skaman82/Pocket-Groundstation/3D files/Cinema4D files/tex/Bildschirmfoto 2018-06-30 um 21.27.20.png

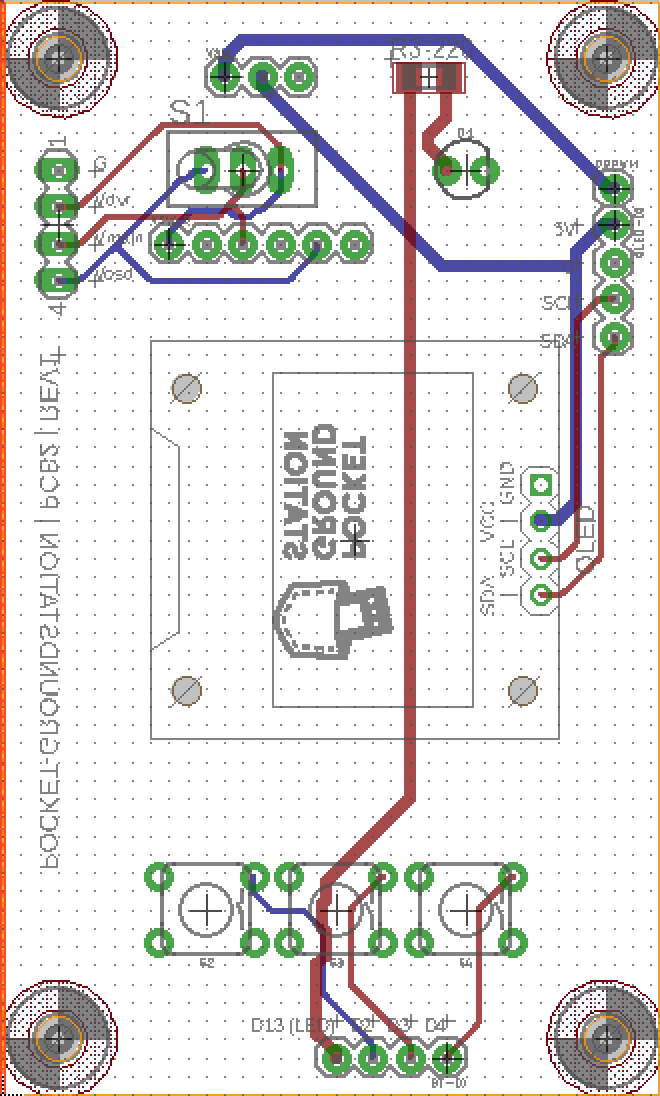
3D files/Cinema4D files/tex/Bildschirmfoto 2018-06-30 um 21.27.20.png
