skaman82/Pocket-Groundstation/3D files/Cinema4D files/tex/Bildschirmfoto 2018-07-01 um 21.55.06.png

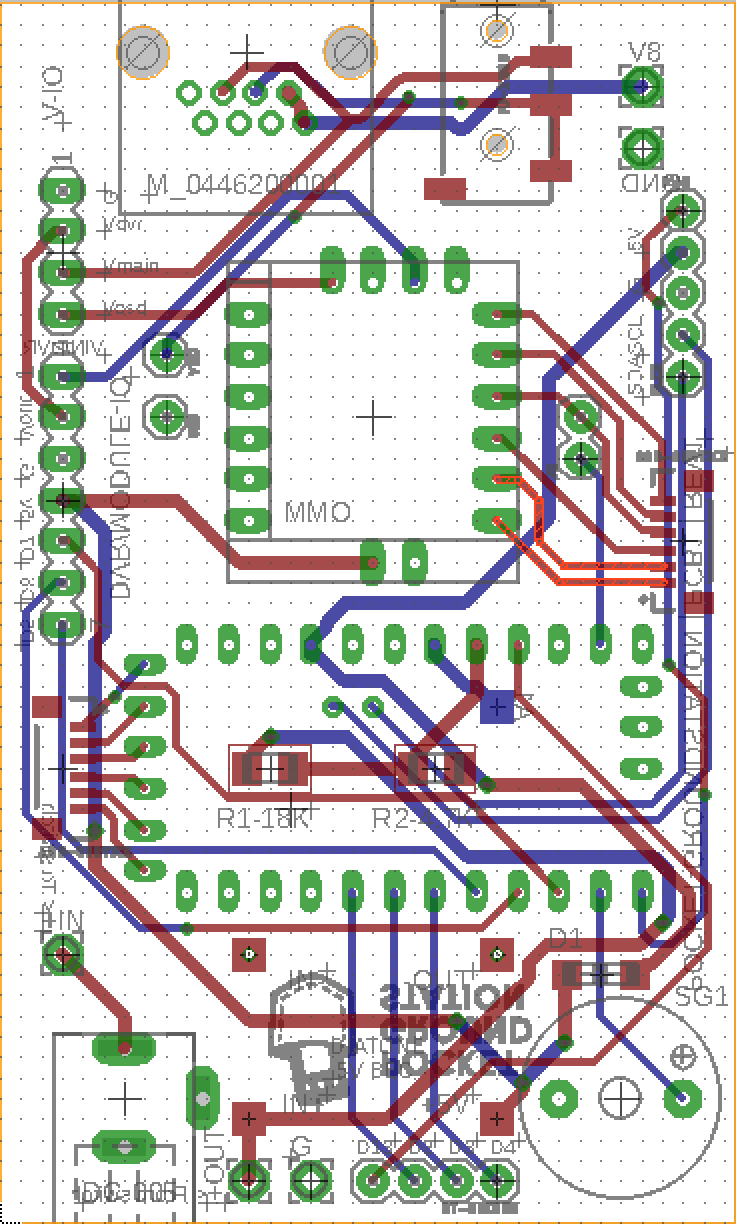
3D files/Cinema4D files/tex/Bildschirmfoto 2018-07-01 um 21.55.06.png
