skaman82/Pocket-Groundstation/3D files/Cinema4D files/tex/Bildschirmfoto 2018-07-02 um 12.51.13.png

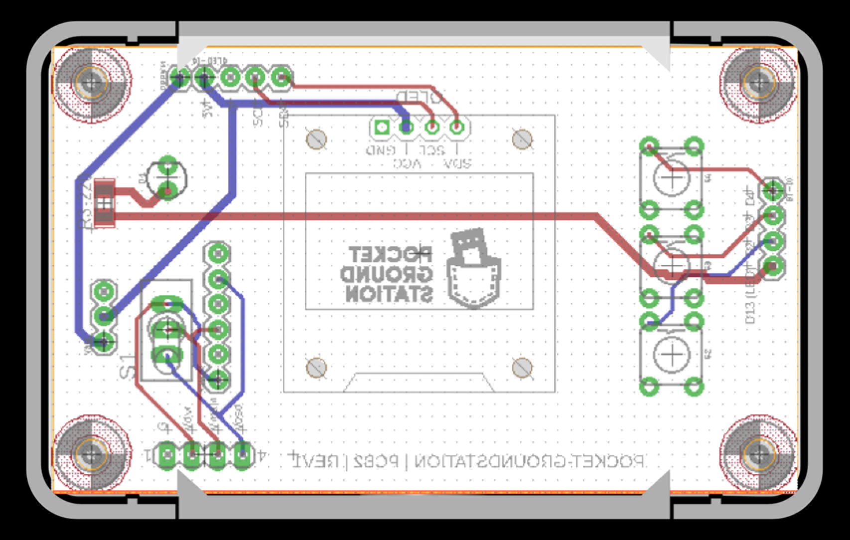
3D files/Cinema4D files/tex/Bildschirmfoto 2018-07-02 um 12.51.13.png
