skaman82/Pocket-Groundstation/3D files/Cinema4D files/tex/downImg.png

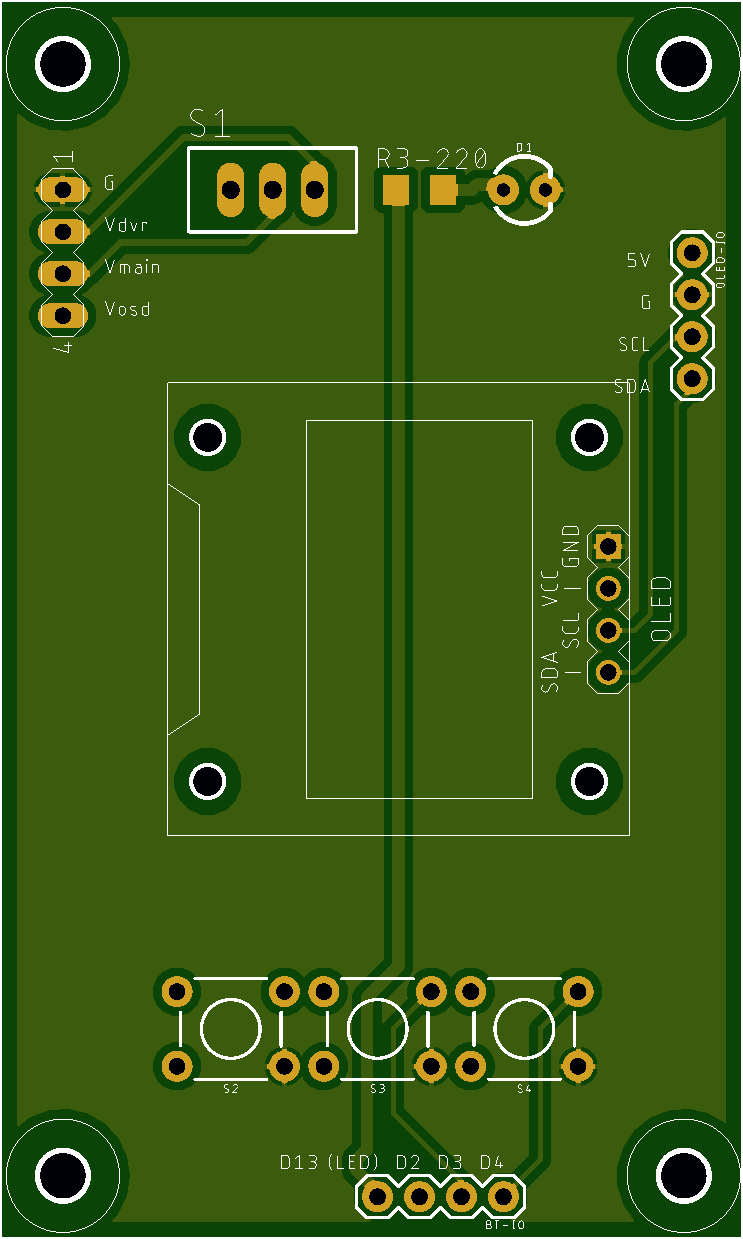
3D files/Cinema4D files/tex/downImg.png
