skaman82/Pocket-Groundstation/OSD-Code/max7456library/examples/CharsetLoader/charset.bmp

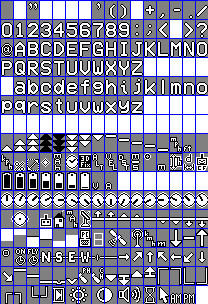
OSD-Code/max7456library/examples/CharsetLoader/charset.bmp
