skaman82/Pocket-Groundstation/PCB Files/Gerber Files/Module-PCB_v1_t.png

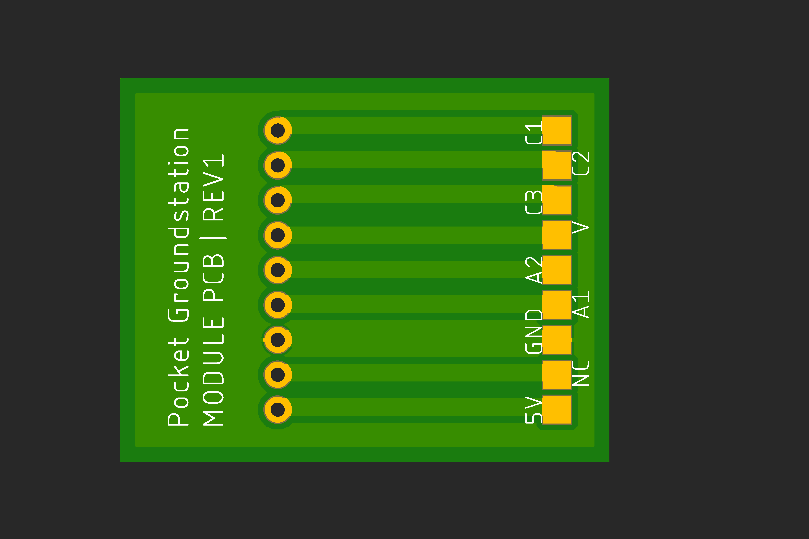
PCB Files/Gerber Files/Module-PCB_v1_t.png
