skaman82/Pocket-Groundstation/PCB Files/Gerber Files/PCB 1_bottom.png

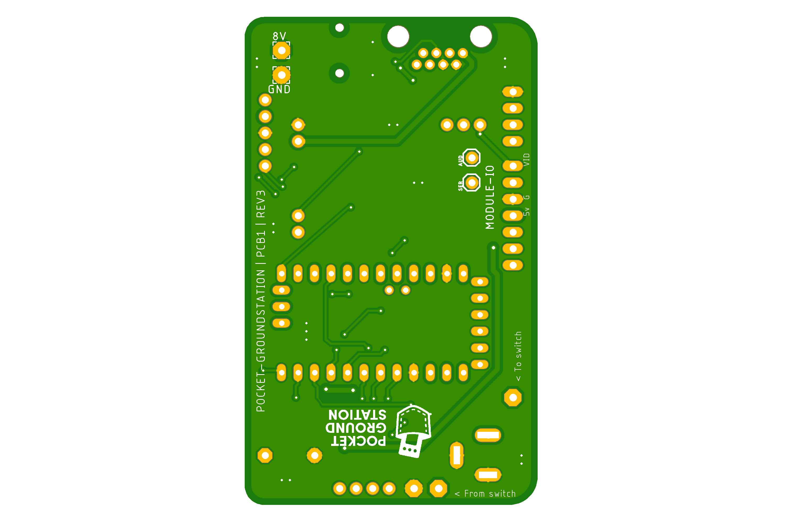
PCB Files/Gerber Files/PCB 1_bottom.png
