skaman82/Pocket-Groundstation/PCB Files/Gerber Files/PCB 1_V2_b.png

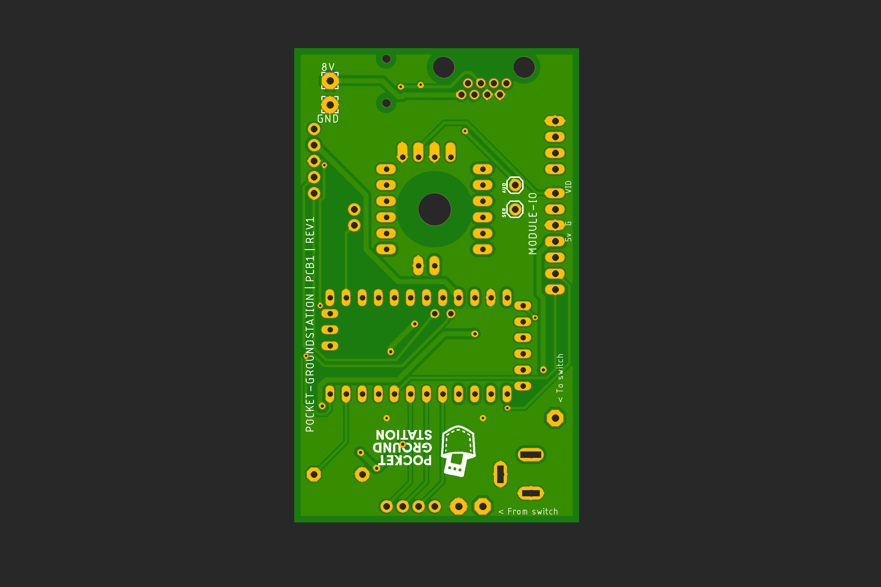
PCB Files/Gerber Files/PCB 1_V2_b.png
