skaman82/Pocket-Groundstation/PCB Files/Gerber Files/PCB 1_V2_t.png

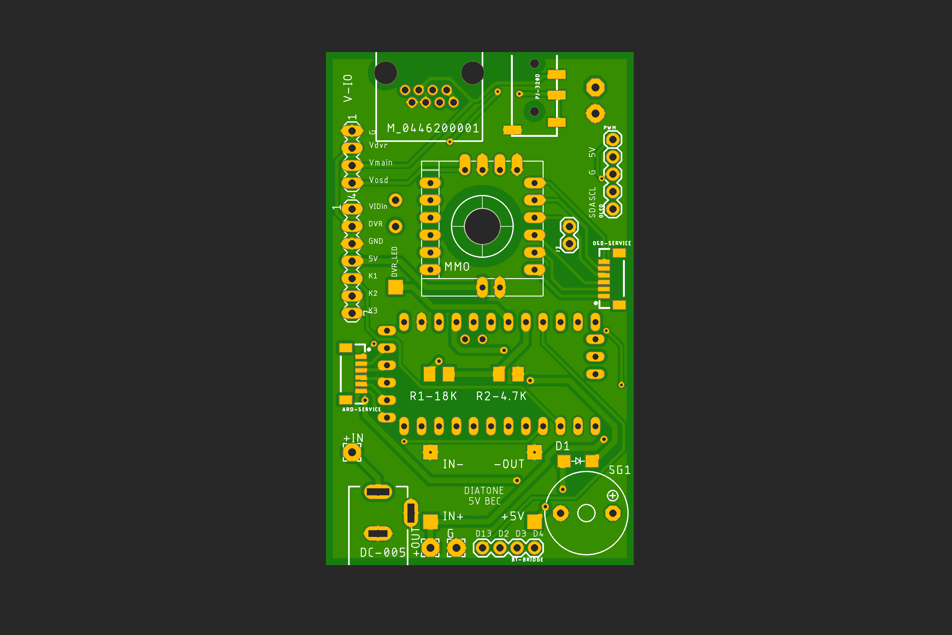
PCB Files/Gerber Files/PCB 1_V2_t.png
