skaman82/Pocket-Groundstation/PCB Files/Gerber Files/PCB 2_bottom.png

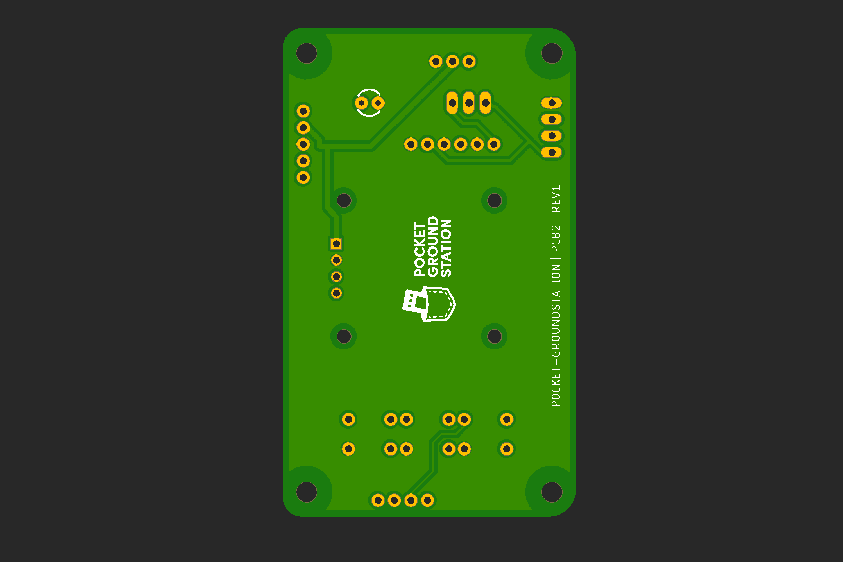
PCB Files/Gerber Files/PCB 2_bottom.png
