skaman82/Pocket-Groundstation/PCB Files/Gerber Files/PCB 2_top.png

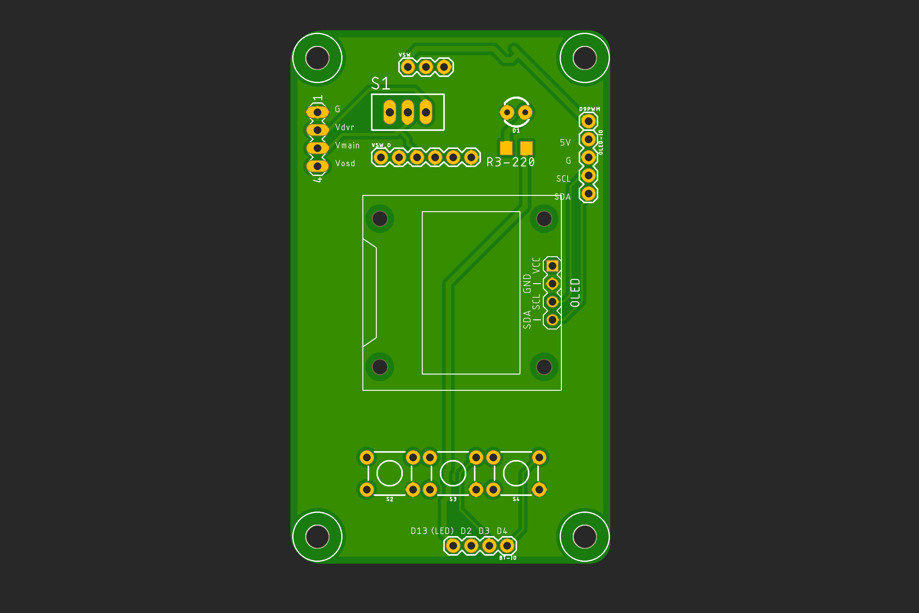
PCB Files/Gerber Files/PCB 2_top.png
