skaman82/Pocket-Groundstation/ARDUINO-Code/bitmaps.h

const unsigned char splash_bitmap[] PROGMEM = 
{
  // size is 96 x 46
  0x00,0x00,0x00,0x00,0x00,0x00,0x00,0x00,0x00,0x00,0x00,0x00, // ................................................................................................
  0x00,0x03,0xC0,0x00,0x00,0x00,0x00,0x00,0x00,0x00,0x00,0x00, // ..............####..............................................................................
  0x00,0x03,0xFE,0x00,0x00,0x00,0x00,0x00,0x00,0x00,0x00,0x00, // ..............#########.........................................................................
  0x00,0x03,0xFF,0xF0,0x00,0x00,0x00,0x00,0x00,0x00,0x00,0x00, // ..............##############....................................................................
  0x00,0x03,0xFF,0xFE,0x00,0x00,0x00,0x00,0x00,0x00,0x00,0x00, // ..............#################.................................................................
  0x00,0x07,0xFF,0xFE,0x00,0x00,0x00,0x00,0x00,0x00,0x00,0x00, // .............##################.................................................................
  0x00,0x07,0x3F,0xFE,0x00,0x00,0x00,0x00,0x00,0x00,0x00,0x00, // .............###..#############.................................................................
  0x00,0x07,0x31,0xFC,0x00,0x00,0x00,0x00,0x00,0x00,0x00,0x00, // .............###..##...#######..................................................................
  0x00,0x07,0xF1,0x9C,0x00,0x00,0x00,0x00,0x00,0x00,0x00,0x00, // .............#######...##..###..................................................................
  0x00,0x07,0xFF,0x9C,0x00,0x00,0x00,0x00,0x00,0x00,0x00,0x00, // .............############..###..................................................................
  0x00,0x0F,0xFF,0xFC,0x00,0x00,0x00,0x00,0x00,0x00,0x00,0x00, // ............##################..................................................................
  0x00,0x0F,0xFF,0xFC,0x00,0x3E,0x1E,0x0F,0x1B,0x3E,0xFE,0x00, // ............##################............#####....####.....####...##.##..#####.#######.........
  0x00,0x0F,0x03,0xF8,0x00,0x3F,0x3F,0x1F,0x9B,0x3E,0xFE,0x00, // ............####......#######.............######..######...######..##.##..#####.#######.........
  0x00,0x0F,0x00,0x78,0x00,0x23,0x63,0xB0,0x9E,0x30,0x10,0x00, // ............####.........####.............#...##.##...###.##....#..####...##.......#............
  0x00,0x0F,0x00,0x78,0x00,0x23,0x61,0xB0,0x1C,0x30,0x10,0x00, // ............####.........####.............#...##.##....##.##.......###....##.......#............
  0x00,0x1E,0x00,0x78,0x00,0x3E,0x41,0xB0,0x1C,0x3E,0x10,0x00, // ...........####..........####.............#####..#.....##.##.......###....#####....#............
  0x00,0x7E,0x00,0x78,0x00,0x3C,0x61,0xB0,0x1E,0x30,0x10,0x00, // .........######..........####.............####...##....##.##.......####...##.......#............
  0x03,0xFE,0x00,0xFE,0x00,0x20,0x73,0x19,0x9F,0x30,0x10,0x00, // ......#########.........#######...........#......###..##...##..##..#####..##.......#............
  0x0F,0xFE,0x00,0xFF,0x80,0x30,0x3F,0x1F,0x9B,0xBE,0x10,0x00, // ....###########.........#########.........##......######...######..##.###.#####....#............
  0x0F,0xFE,0x00,0xFF,0x80,0x00,0x0C,0x06,0x00,0x00,0x00,0x00, // ....###########.........#########...................##.......##.................................
  0x0F,0xFE,0x00,0xFF,0x80,0x00,0x00,0x00,0x00,0x00,0x00,0x00, // ....###########.........#########...............................................................
  0x0C,0x7F,0xFF,0xF1,0x80,0x00,0x00,0x00,0x00,0x00,0x00,0x00, // ....##...###################...##...............................................................
  0x0C,0x00,0xF8,0x01,0x80,0x1F,0x1F,0x0F,0x0C,0xCC,0xCF,0x80, // ....##..........#####..........##..........#####...#####....####....##..##..##..##..#####.......
  0x0D,0x80,0x00,0x05,0x80,0x3F,0x1F,0x9F,0x8C,0xCC,0xCF,0xC0, // ....##.##....................#.##.........######...######..######...##..##..##..##..######......
  0x0C,0x00,0x00,0x01,0x80,0x30,0x19,0xB0,0xCC,0xCE,0xCC,0x60, // ....##.........................##.........##.......##..##.##....##..##..##..###.##..##...##.....
  0x0C,0x00,0x00,0x01,0x80,0x60,0x19,0xB0,0xCC,0xCF,0xCC,0x60, // ....##.........................##........##........##..##.##....##..##..##..######..##...##.....
  0x0C,0x00,0x00,0x01,0x80,0x67,0x9F,0x30,0xCC,0xCF,0xCC,0x60, // ....##.........................##........##..####..#####..##....##..##..##..######..##...##.....
  0x04,0x80,0x00,0x0D,0x80,0x61,0x9E,0x30,0xCC,0xCD,0xCC,0x60, // .....#..#...................##.##........##....##..####...##....##..##..##..##.###..##...##.....
  0x04,0x80,0x00,0x0D,0x80,0x3B,0x9B,0x1D,0xCD,0xCC,0xCC,0xC0, // .....#..#...................##.##.........###.###..##.##...###.###..##.###..##..##..##..##......
  0x04,0x00,0x00,0x01,0x80,0x1F,0x1B,0x0F,0x87,0x8C,0xCF,0xC0, // .....#.........................##..........#####...##.##....#####....####...##..##..######......
  0x04,0x00,0x00,0x01,0x80,0x00,0x00,0x00,0x00,0x00,0x00,0x00, // .....#.........................##...............................................................
  0x06,0x80,0x00,0x09,0x80,0x00,0x00,0x00,0x00,0x00,0x00,0x00, // .....##.#...................#..##...............................................................
  0x06,0x80,0x00,0x09,0x00,0x00,0x00,0x00,0x00,0x00,0x00,0x00, // .....##.#...................#..#................................................................
  0x06,0x80,0x00,0x09,0x00,0x3C,0xFC,0x67,0xF6,0x3E,0x33,0x00, // .....##.#...................#..#..........####..######...##..#######.##...#####...##..##........
  0x06,0x00,0x00,0x01,0x00,0x76,0x30,0xE1,0xC6,0x77,0x3B,0x00, // .....##........................#.........###.##...##....###....###...##..###.###..###.##........
  0x06,0x00,0x00,0x01,0x00,0x60,0x30,0xF0,0x86,0xC3,0x3B,0x00, // .....##........................#.........##.......##....####....#....##.##....##..###.##........
  0x06,0x40,0x00,0x1B,0x00,0x3C,0x31,0xB0,0xC6,0xC1,0xBF,0x00, // .....##..#.................##.##..........####....##...##.##....##...##.##.....##.######........
  0x06,0x60,0x00,0x33,0x00,0x1E,0x31,0xF8,0xC6,0xC1,0xB7,0x00, // .....##..##...............##..##...........####...##...######...##...##.##.....##.##.###........
  0x07,0x80,0x00,0x07,0x00,0x06,0x31,0xF8,0xC6,0xE3,0x37,0x00, // .....####....................###.............##...##...######...##...##.###...##..##.###........
  0x01,0xC6,0x03,0x9E,0x00,0x76,0x33,0x18,0xC6,0x7F,0x33,0x00, // .......###...##.......###..####..........###.##...##..##...##...##...##..#######..##..##........
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
}
;




const unsigned char settings42_bitmap[] PROGMEM = 
{
  // size is 42 x 35
 0x00,0x00,0x00,0x00,0x00,0x00, // ................................................
  0x00,0x00,0x3E,0x00,0x00,0x00, // ..................#####.........................
  0x00,0x00,0x7F,0x00,0x00,0x00, // .................#######........................
  0x00,0x00,0x7F,0x00,0x00,0x00, // .................#######........................
  0x00,0x30,0xFF,0x86,0x00,0x00, // ..........##....#########....##.................
  0x00,0x7F,0xFF,0xFF,0x00,0x00, // .........#######################................
  0x00,0xFF,0xFF,0xFF,0x80,0x00, // ........#########################...............
  0x01,0xFF,0xC1,0xFF,0xC0,0x00, // .......###########.....###########..............
  0x01,0xFF,0x00,0x7F,0xC0,0x00, // .......#########.........#########..............
  0x00,0xFE,0x1C,0x3F,0x80,0x00, // ........#######....###....#######...............
  0x00,0xFC,0x7F,0x1F,0x80,0x00, // ........######...#######...######...............
  0x00,0xF8,0xFF,0x8F,0x80,0x00, // ........#####...#########...#####...............
  0x00,0xF1,0xC1,0xC7,0x80,0x00, // ........####...###.....###...####...............
  0x01,0xE3,0x80,0xE3,0xC0,0x00, // .......####...###.......###...####..............
  0x03,0xE7,0x00,0x73,0xE0,0x00, // ......#####..###.........###..#####.............
  0x0F,0xE6,0x08,0x33,0xF8,0x00, // ....#######..##.....#.....##..#######...........
  0x0F,0xCE,0x08,0x39,0xF8,0x00, // ....######..###.....#.....###..######...........
  0x0F,0xCE,0x3E,0x39,0xF8,0x00, // ....######..###...#####...###..######...........
  0x0F,0xCE,0x08,0x39,0xF8,0x00, // ....######..###.....#.....###..######...........
  0x0F,0xE6,0x08,0x33,0xF8,0x00, // ....#######..##.....#.....##..#######...........
  0x03,0xE7,0x00,0x73,0xE0,0x00, // ......#####..###.........###..#####.............
  0x01,0xF3,0x80,0xE3,0xC0,0x00, // .......#####..###.......###...####..............
  0x00,0xF1,0xC1,0xC7,0x80,0x00, // ........####...###.....###...####...............
  0x00,0xF8,0xFF,0x8F,0x80,0x00, // ........#####...#########...#####...............
  0x00,0xFC,0x7F,0x1F,0x80,0x00, // ........######...#######...######...............
  0x00,0xFE,0x1C,0x3F,0x80,0x00, // ........#######....###....#######...............
  0x01,0xFF,0x00,0x7F,0xC0,0x00, // .......#########.........#########..............
  0x01,0xFF,0xC1,0xFF,0xC0,0x00, // .......###########.....###########..............
  0x00,0xFF,0xFF,0xFF,0x80,0x00, // ........#########################...............
  0x00,0x7F,0xFF,0xFF,0x00,0x00, // .........#######################................
  0x00,0x30,0xFF,0x86,0x00,0x00, // ..........##....#########....##.................
  0x00,0x00,0x7F,0x00,0x00,0x00, // .................#######........................
  0x00,0x00,0x7F,0x00,0x00,0x00, // .................#######........................
  0x00,0x00,0x3E,0x00,0x00,0x00, // ..................#####.........................
  0x00,0x00,0x00,0x00,0x00,0x00  // ................................................
}
;



const unsigned char DVR42_bitmap[] PROGMEM = 
{
  // size is 42 x 35
  0x00,0x00,0x00,0x00,0x00,0x00, // ................................................
  0x00,0x00,0x00,0x00,0x00,0x00, // ................................................
  0x00,0x00,0x00,0x00,0x00,0x00, // ................................................
  0x00,0x00,0x00,0x00,0x00,0x00, // ................................................
  0x00,0x00,0x00,0x00,0x00,0x00, // ................................................
  0x00,0x00,0x00,0x00,0x00,0x00, // ................................................
  0x1F,0xFF,0x0F,0x80,0x00,0x00, // ...#############....#####.......................
  0x20,0x00,0x88,0x40,0x00,0x00, // ..#.............#...#....#......................
  0x20,0x00,0x78,0x20,0x00,0x00, // ..#..............####.....#.....................
  0x20,0x00,0x00,0x1F,0xFE,0x00, // ..#........................############.........
  0x20,0x00,0x00,0x00,0x01,0x00, // ..#....................................#........
  0x20,0x00,0x00,0x00,0x01,0x00, // ..#....................................#........
  0x20,0xFF,0xFF,0x03,0xFD,0x00, // ..#.....################......########.#........
  0x21,0xFF,0xFF,0x83,0xFD,0x00, // ..#....##################.....########.#........
  0x21,0xFD,0xFF,0x80,0x01,0x00, // ..#....#######.##########..............#........
  0x21,0xFC,0xFF,0x80,0x01,0x00, // ..#....#######..#########..............#........
  0x21,0xFC,0x7F,0x83,0xFD,0x00, // ..#....#######...########.....########.#........
  0x21,0xFC,0x3F,0x83,0xFD,0x00, // ..#....#######....#######.....########.#........
  0x21,0xFC,0x1F,0x80,0x01,0x00, // ..#....#######.....######..............#........
  0x21,0xFC,0x3F,0x80,0x01,0x00, // ..#....#######....#######..............#........
  0x21,0xFC,0x7F,0x83,0xFD,0x00, // ..#....#######...########.....########.#........
  0x21,0xFC,0xFF,0x83,0xFD,0x00, // ..#....#######..#########.....########.#........
  0x21,0xFD,0xFF,0x80,0x01,0x00, // ..#....#######.##########..............#........
  0x21,0xFF,0xFF,0x80,0x01,0x00, // ..#....##################..............#........
  0x20,0xFF,0xFF,0x03,0xFD,0x00, // ..#.....################......########.#........
  0x20,0x00,0x00,0x03,0xFD,0x00, // ..#...........................########.#........
  0x20,0x00,0x00,0x00,0x01,0x00, // ..#....................................#........
  0x20,0xF3,0xCF,0x00,0x01,0x00, // ..#.....####..####..####...............#........
  0x20,0xF3,0xCF,0x03,0xFD,0x00, // ..#.....####..####..####......########.#........
  0x20,0x00,0x00,0x03,0xFD,0x00, // ..#...........................########.#........
  0x20,0x00,0x00,0x00,0x01,0x00, // ..#....................................#........
  0x20,0x00,0x00,0x00,0x01,0x00, // ..#....................................#........
  0x1F,0xFF,0xFF,0xFF,0xFE,0x00, // ...####################################.........
  0x00,0x00,0x00,0x00,0x00,0x00, // ................................................
  0x00,0x00,0x00,0x00,0x00,0x00  // ................................................
}
;


const unsigned char EXIT_bitmap[] PROGMEM = 
{
  // size is 42 x 35
  0x00,0x00,0x00,0x00,0x00,0x00, // ................................................
  0x00,0x00,0x00,0x00,0x00,0x00, // ................................................
  0x00,0x00,0x00,0x00,0x00,0x00, // ................................................
  0x00,0x00,0x00,0x00,0x00,0x00, // ................................................
  0x00,0x00,0x00,0x00,0x00,0x00, // ................................................
  0x00,0x01,0xFF,0xFF,0x00,0x00, // ...............#################................
  0x00,0x03,0xFF,0xFF,0x80,0x00, // ..............###################...............
  0x00,0x06,0x00,0x00,0xC0,0x00, // .............##.................##..............
  0x00,0x06,0x00,0x00,0xC0,0x00, // .............##.................##..............
  0x00,0x06,0x00,0x00,0xC0,0x00, // .............##.................##..............
  0x00,0x06,0x00,0x00,0xC0,0x00, // .............##.................##..............
  0x00,0x40,0x00,0x00,0xC0,0x00, // .........#......................##..............
  0x00,0xC0,0x00,0x00,0xC0,0x00, // ........##......................##..............
  0x01,0xC0,0x00,0x00,0xC0,0x00, // .......###......................##..............
  0x03,0xC0,0x00,0x00,0xC0,0x00, // ......####......................##..............
  0x07,0xFF,0xFF,0x80,0xC0,0x00, // .....####################.......##..............
  0x0F,0xFF,0xFF,0x80,0xC0,0x00, // ....#####################.......##..............
  0x1F,0xFF,0xFF,0x80,0xC0,0x00, // ...######################.......##..............
  0x0F,0xFF,0xFF,0x80,0xC0,0x00, // ....#####################.......##..............
  0x07,0xFF,0xFF,0x80,0xC0,0x00, // .....####################.......##..............
  0x03,0xC0,0x00,0x00,0xC0,0x00, // ......####......................##..............
  0x01,0xC0,0x00,0x00,0xC0,0x00, // .......###......................##..............
  0x00,0xC0,0x00,0x00,0xC0,0x00, // ........##......................##..............
  0x00,0x40,0x00,0x00,0xC0,0x00, // .........#......................##..............
  0x00,0x06,0x00,0x00,0xC0,0x00, // .............##.................##..............
  0x00,0x06,0x00,0x00,0xC0,0x00, // .............##.................##..............
  0x00,0x06,0x00,0x00,0xC0,0x00, // .............##.................##..............
  0x00,0x06,0x00,0x00,0xC0,0x00, // .............##.................##..............
  0x00,0x03,0xFF,0xFF,0x80,0x00, // ..............###################...............
  0x00,0x01,0xFF,0xFF,0x00,0x00, // ...............#################................
  0x00,0x00,0x00,0x00,0x00,0x00, // ................................................
  0x00,0x00,0x00,0x00,0x00,0x00, // ................................................
  0x00,0x00,0x00,0x00,0x00,0x00, // ................................................
  0x00,0x00,0x00,0x00,0x00,0x00, // ................................................
  0x00,0x00,0x00,0x00,0x00,0x00  // ................................................
}
;

   

const uint8_t DVRstatus8_bitmap[] U8G_PROGMEM = 
{
  // size is 8  x 8
  0x7E, // .######.
  0x81, // #......#
  0x99, // #..##..#
  0xBD, // #.####.#
  0xBD, // #.####.#
  0x99, // #..##..#
  0x81, // #......#
  0x7E  // .######.
 }
;


const unsigned char DVR_bitmap[] PROGMEM = {
    // size is 16  x 8
  0x7C,0x40, // .#####...#......
  0xFE,0xC0, // #######.##......
  0xC7,0xC0, // ##...#####......
  0xD7,0xC0, // ##.#.#####......
  0xC7,0xC0, // ##...#####......
  0xD7,0xC0, // ##.#.#####......
  0xFE,0xC0, // #######.##......
  0x7C,0x40  // .#####...#......
};


const unsigned char OSD_bitmap[] PROGMEM = {
    // size is 10  x 8
    0x7F,0x80, // .########.......
    0x80,0x40, // #........#......
    0x80,0x40, // #........#......
    0x87,0x40, // #....###.#......
    0x80,0x40, // #........#......
    0x87,0x40, // #....###.#......
    0x80,0x40, // #........#......
    0x7F,0x80  // .########.......
};


const unsigned char RSSI_bitmap[] PROGMEM = {
    // size is 10  x 8
    0x60,0x00, // .##.............
    0x60,0x00, // .##.............
    0x6C,0x00, // .##.##..........
    0x6C,0x00, // .##.##..........
    0x6C,0x00, // .##.##..........
    0x6D,0x80, // .##.##.##.......
    0x6D,0x80, // .##.##.##.......
    0xFF,0xC0  // ##########......
};

const uint8_t back_bitmap[] PROGMEM = {
    // size is 10  x 8
    0x00,0x00, // ................
    0x08,0x00, // ....#...........
    0x18,0x00, // ...##...........
    0x3F,0xC0, // ..########......
    0x7F,0xC0, // .#########......
    0x3F,0xC0, // ..########......
    0x18,0x00, // ...##...........
    0x08,0x00  // ....#...........
};
